JMike360/ece477/final/main/bt.c

/*
   This example code is in the Public Domain (or CC0 licensed, at your option.)

   Unless required by applicable law or agreed to in writing, this
   software is distributed on an "AS IS" BASIS, WITHOUT WARRANTIES OR
   CONDITIONS OF ANY KIND, either express or implied.
*/

#include <stdint.h>
#include <string.h>
#include <stdbool.h>
#include <stdio.h>
#include "nvs.h"
#include "nvs_flash.h"
#include "freertos/FreeRTOS.h"
#include "freertos/task.h"
#include "esp_log.h"
#include "esp_bt.h"
#include "esp_bt_main.h"
#include "esp_gap_bt_api.h"
#include "esp_bt_device.h"
#include "esp_spp_api.h"
#include "../include/bt.h"
#include "../include/cmd.h"
#include "../include/my_rsa.h"

#include "time.h"
#include "sys/time.h"

#define SPP_TAG "SPP_ACCEPTOR_DEMO"
#define SPP_SERVER_NAME "SPP_SERVER"
#define EXAMPLE_DEVICE_NAME "ESP_SPP_ACCEPTOR"
#define SPP_SHOW_DATA 0
#define SPP_SHOW_SPEED 1
#define SPP_SHOW_MODE SPP_SHOW_DATA    /*Choose show mode: show data or speed*/

static const esp_spp_mode_t esp_spp_mode = ESP_SPP_MODE_CB;

static const esp_spp_sec_t sec_mask = ESP_SPP_SEC_AUTHENTICATE;
static const esp_spp_role_t role_slave = ESP_SPP_ROLE_SLAVE;

static uint32_t deviceHandle=0;

void btSendData(uint8_t* data, int encryptMsg, int len) {
    if (deviceHandle == 0)
        return;

    if (encryptMsg) {
        uint8_t* encrypted_data = NULL;
        if (my_rsa_encrypt(data, &encrypted_data) == RSA_FAILURE)
            return;
        uint8_t* bufferToSend = malloc(KEYSIZE / 8 + 1);
        memcpy(bufferToSend, encrypted_data, 256);
        bufferToSend[KEYSIZE / 8] = '\n';
        esp_spp_write(deviceHandle, KEYSIZE / 8 + 1, bufferToSend);
        free(encrypted_data);
        free(bufferToSend);
    }
    else
        esp_spp_write(deviceHandle, len, data);
}

static void esp_spp_cb(esp_spp_cb_event_t event, esp_spp_cb_param_t *param)
{
    switch (event) {
    case ESP_SPP_INIT_EVT:
        ESP_LOGI(SPP_TAG, "ESP_SPP_INIT_EVT");
        esp_bt_dev_set_device_name(EXAMPLE_DEVICE_NAME);
        esp_bt_gap_set_scan_mode(ESP_BT_CONNECTABLE, ESP_BT_GENERAL_DISCOVERABLE);
        esp_spp_start_srv(sec_mask,role_slave, 0, SPP_SERVER_NAME);
        break;
    case ESP_SPP_DISCOVERY_COMP_EVT:
        ESP_LOGI(SPP_TAG, "ESP_SPP_DISCOVERY_COMP_EVT");
        break;
    case ESP_SPP_OPEN_EVT:
        ESP_LOGI(SPP_TAG, "ESP_SPP_OPEN_EVT");
        break;
    case ESP_SPP_CLOSE_EVT://断开连接会触发这个事件
        ESP_LOGI(SPP_TAG, "ESP_SPP_CLOSE_EVT");
        deviceHandle=0;
        break;
    case ESP_SPP_START_EVT:
        ESP_LOGI(SPP_TAG, "ESP_SPP_START_EVT");
        break;
    case ESP_SPP_CL_INIT_EVT:
        ESP_LOGI(SPP_TAG, "ESP_SPP_CL_INIT_EVT");
        break;
    case ESP_SPP_DATA_IND_EVT:
        ESP_LOGI(SPP_TAG, "ESP_SPP_DATA_IND_EVT len=%d handle=%d",
                 param->data_ind.len, param->data_ind.handle);
        esp_log_buffer_hex("",param->data_ind.data,param->data_ind.len);
        doCMD(param->data_ind.data, BT_MODE);
        break;
    case ESP_SPP_CONG_EVT:
        ESP_LOGI(SPP_TAG, "ESP_SPP_CONG_EVT");
        break;
    case ESP_SPP_WRITE_EVT:
        ESP_LOGI(SPP_TAG, "ESP_SPP_WRITE_EVT");
        break;
    case ESP_SPP_SRV_OPEN_EVT: //打开设备
        ESP_LOGI(SPP_TAG, "ESP_SPP_SRV_OPEN_EVT");
        deviceHandle=param->srv_open.handle; //储存这个句柄
        ESP_LOGI(SPP_TAG, "handle:%d\n",deviceHandle);
        break;
    default:
        break;
    }
}

static void esp_bt_gap_cb(esp_bt_gap_cb_event_t event, esp_bt_gap_cb_param_t *param)
{
    switch (event) {
        case ESP_BT_GAP_AUTH_CMPL_EVT:{
            if (param->auth_cmpl.stat == ESP_BT_STATUS_SUCCESS) {
                ESP_LOGI(SPP_TAG, "authentication success: %s", param->auth_cmpl.device_name);
                esp_log_buffer_hex(SPP_TAG, param->auth_cmpl.bda, ESP_BD_ADDR_LEN);
            } else {
                ESP_LOGE(SPP_TAG, "authentication failed, status:%d", param->auth_cmpl.stat);
            }
            break;
        }
        case ESP_BT_GAP_PIN_REQ_EVT:{
            ESP_LOGI(SPP_TAG, "ESP_BT_GAP_PIN_REQ_EVT min_16_digit:%d", param->pin_req.min_16_digit);
            if (param->pin_req.min_16_digit) {
                ESP_LOGI(SPP_TAG, "Input pin code: 0000 0000 0000 0000");
                esp_bt_pin_code_t pin_code = {0};
                esp_bt_gap_pin_reply(param->pin_req.bda, true, 16, pin_code);
            } else {
                ESP_LOGI(SPP_TAG, "Input pin code: 1234");
                esp_bt_pin_code_t pin_code;
                pin_code[0] = '1';
                pin_code[1] = '2';
                pin_code[2] = '3';
                pin_code[3] = '4';
                esp_bt_gap_pin_reply(param->pin_req.bda, true, 4, pin_code);
            }
            break;
        }

    #if (CONFIG_BT_SSP_ENABLED == true)
        case ESP_BT_GAP_CFM_REQ_EVT:
            ESP_LOGI(SPP_TAG, "ESP_BT_GAP_CFM_REQ_EVT Please compare the numeric value: %d", param->cfm_req.num_val);
            esp_bt_gap_ssp_confirm_reply(param->cfm_req.bda, true);
            break;
        case ESP_BT_GAP_KEY_NOTIF_EVT:
            ESP_LOGI(SPP_TAG, "ESP_BT_GAP_KEY_NOTIF_EVT passkey:%d", param->key_notif.passkey);
            break;
        case ESP_BT_GAP_KEY_REQ_EVT:
            ESP_LOGI(SPP_TAG, "ESP_BT_GAP_KEY_REQ_EVT Please enter passkey!");
            break;
    #endif

        default: {
            ESP_LOGI(SPP_TAG, "event: %d", event);
            break;
        }
    }
    return;
}

void btInit() {
    esp_err_t ret = nvs_flash_init();
    if (ret == ESP_ERR_NVS_NO_FREE_PAGES || ret == ESP_ERR_NVS_NEW_VERSION_FOUND) {
        ESP_ERROR_CHECK(nvs_flash_erase());
        ret = nvs_flash_init();
    }
    ESP_ERROR_CHECK( ret );

    ESP_ERROR_CHECK(esp_bt_controller_mem_release(ESP_BT_MODE_BLE));

    esp_bt_controller_config_t bt_cfg = BT_CONTROLLER_INIT_CONFIG_DEFAULT();
    if ((ret = esp_bt_controller_init(&bt_cfg)) != ESP_OK) {
        ESP_LOGE(SPP_TAG, "%s initialize controller failed: %s\n", __func__, esp_err_to_name(ret));
        return;
    }

    if ((ret = esp_bt_controller_enable(ESP_BT_MODE_CLASSIC_BT)) != ESP_OK) {
        ESP_LOGE(SPP_TAG, "%s enable controller failed: %s\n", __func__, esp_err_to_name(ret));
        return;
    }

    if ((ret = esp_bluedroid_init()) != ESP_OK) {
        ESP_LOGE(SPP_TAG, "%s initialize bluedroid failed: %s\n", __func__, esp_err_to_name(ret));
        return;
    }

    if ((ret = esp_bluedroid_enable()) != ESP_OK) {
        ESP_LOGE(SPP_TAG, "%s enable bluedroid failed: %s\n", __func__, esp_err_to_name(ret));
        return;
    }
}

void btRegister() {
    esp_err_t ret = ESP_OK;

    if ((ret = esp_bt_gap_register_callback(esp_bt_gap_cb)) != ESP_OK) {
        ESP_LOGE(SPP_TAG, "%s gap register failed: %s\n", __func__, esp_err_to_name(ret));
        return;
    }

    if ((ret = esp_spp_register_callback(esp_spp_cb)) != ESP_OK) {
        ESP_LOGE(SPP_TAG, "%s spp register failed: %s\n", __func__, esp_err_to_name(ret));
        return;
    }
    
    if ((ret = esp_spp_init(esp_spp_mode)) != ESP_OK) {
        ESP_LOGE(SPP_TAG, "%s spp init failed: %s\n", __func__, esp_err_to_name(ret));
        return;
    }
}

void btSetPairing() {
    #if (CONFIG_BT_SSP_ENABLED == true)
    /* Set default parameters for Secure Simple Pairing */
    esp_bt_sp_param_t param_type = ESP_BT_SP_IOCAP_MODE;
    esp_bt_io_cap_t iocap = ESP_BT_IO_CAP_IO;
    esp_bt_gap_set_security_param(param_type, &iocap, sizeof(uint8_t));
#endif

    /*
     * Set default parameters for Legacy Pairing
     * Use variable pin, input pin code when pairing
     */
    esp_bt_pin_type_t pin_type = ESP_BT_PIN_TYPE_VARIABLE;
    esp_bt_pin_code_t pin_code;
    esp_bt_gap_set_pin(pin_type, 0, pin_code);
}
